MrBlahhhh/esp32-shield-can1-can2-kdcan-analogin-sdcard/fab/order-tht-paste.txt

C10790,5
C131334,20
C158038,10
C35449,10
C474881,20
C474882,10
