MrBlahhhh/esp32-shield-can1-can2-kdcan-analogin-sdcard/fab/order-lcsc-paste.txt

C49678,80
C17414,100
C149504,100
C408389,50
C17513,100
C13967,60
C134976,30
C223989,30
C5159707,50
C865368,60
C17634,100
C72998,100
C2930178,100
C13585,40
C1744,50
C12891,40
C107110,100
C76584,12
C719178,15
C8545,50
C17673,100
C13612,15
C58988,11
C37593,11
C28233,50
C28323,30
C46653,40
C2480,50
C223993,10
C2297,50
C81034,30
C719027,6
C17313,10
C7472914,10
C17408,100
C17713,100
C17901,100
C17955,50
C17560,100
C17985,100
C17695,100
C17506,100
C17828,100
C17514,100
C127592,10
C7484,10
C626759,6
C5186937,10
