MrBlahhhh/esp32-shield-can1-can2-kdcan-analogin-sdcard/fwsim/shim/sim.cpp

#include "sim.h"

#include <stdio.h>
#include <stdlib.h>
#include <stdarg.h>
#include <string.h>
#include <math.h>
#include <map>
#include <set>
#include <algorithm>
#include <fstream>
#include <sstream>

namespace sim {

// ===========================================================================
// Board profiles
//
// Two boards, because the interesting question is not "does this sketch work"
// -- it demonstrably works on the car -- but "what does this sketch do when the
// pins underneath it change". The autosport map is README section 6 verbatim;
// the divider ratios are section 3.

static const double R_BYPASS = 1.0000;   // 0-3.3 V, 10k shorted
static const double R_5V     = 0.5769;   // 0-5 V,  15/26 (s3zero only now)
static const double R_16V    = 0.1673;   // 0-16 V, 2.21/13.21 -- the only
                                         // ratio on the carrier board

static Board make_s3zero() {
  Board b;
  b.name = "s3zero";
  const PinDef pins[] = {
      // The R53 shift-light board: a Waveshare ESP32-S3-Zero, an SN65HVD230,
      // an 8-LED strip and a 10k/10k divider on the wideband.
      {1, ROLE_ANALOG_IN,  "WIDEBAND", 0.5, RAIL_NONE},
      {4, ROLE_WS2812_DIN, "LED_DIN",  0.0, RAIL_NONE},
      {5, ROLE_CAN_TX,     "CAN_TX",   0.0, RAIL_NONE},
      {6, ROLE_CAN_RX,     "CAN_RX",   0.0, RAIL_NONE},
      {7, ROLE_I2C_SDA,    "SDA",      0.0, RAIL_NONE},
      {8, ROLE_I2C_SCL,    "SCL",      0.0, RAIL_NONE},
  };
  b.pins.assign(pins, pins + sizeof(pins) / sizeof(pins[0]));
  b.adc_fullscale = 3.10;
  b.adc_gain_err = 0.015;    // internal ADC, +-1-2% even calibrated
  b.adc_bits = 12;
  b.ws2812_buffered = false;
  b.has_pwr_fail = false;
  b.pwr_fail_trip = 0.0;
  b.pwr_fail_hyst = 0.0;
  b.supply_floor = 0.0;
  b.ridethru_shed_ms = 20.0;   // a dev board's decoupling, nothing more
  b.ridethru_noshed_ms = 20.0;
  return b;
}
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
